WRansohoff/MotoMate/firmware/v1_testsuite/src/main.c

// Vendor-provided device header file.
#include "stm32l4xx.h"

// Global definitions.
#include "global.h"

// BSP include.
#include "hal/motomate_v1.h"

// Project includes.
#include "app.h"

/**
 * Main program.
 */
int main(void) {
  // Call the high-level 'board_init' method to set up pins and
  // peripherals. The method can be found in the BSP header file,
  // currently `../../fw_lib/bsp/hal/motomate_v1.h`
  board_init();

  // Main application loop.
  while (1) {
    // Wait for an ongoing display DMA transfer operation to complete
    // before modifying the framebuffer.
    while ( ( DMA1_Channel3->CCR & DMA_CCR_EN ) ) { __WFI(); }

    // Re-draw the framebuffer.
    redraw_fb();

    // Re-trigger a DMA transfer to draw to the display.
    DMA1_Channel3->CCR |=  ( DMA_CCR_EN );

    if ( cur_mode == MODE_MAIN_MENU ||
         cur_mode == MODE_AUDIO ||
         cur_mode == MODE_BACKLIGHT ||
         cur_mode == MODE_TOUCH ||
         cur_mode == MODE_SD_CARD ||
         cur_mode == MODE_USB ) {
      // Wait for a button press before continuing.
      while ( new_button_presses[ 0 ] == BTN_NONE ) { __WFI(); }
      // Process button input(s).
      process_buttons();
    }
    else if ( cur_mode == MODE_GPS_RX ) {
      // Wait for a button press or new GPS messages before continuing.
      while ( new_button_presses[ 0 ] == BTN_NONE &&
              !new_gps_messages ) {
        __WFI();
      }
      // Process button input(s), if any.
      process_buttons();
      new_gps_messages = 0;
    }
    else if ( cur_mode == MODE_BATTERY ) {
      // TODO: Periodically re-read the ADC value and update.
      // Wait for a button press before continuing.
      while ( new_button_presses[ 0 ] == BTN_NONE ) { __WFI(); }
      // Process button input(s).
      process_buttons();
    }
  }
}
